calimero921/sensor_tab/src/main.h

/*
*/

#include "Arduino.h"

// See the following for generating UUIDs:
// https://www.uuidgenerator.net/
#define SERVICE_UUID "4fafc201-1fb5-459e-8fcc-c5c9c331914b"
#define LED_CHARACTERISTIC_UUID "beb5483e-36e1-4688-b7f5-ea07361b26a8"
#define RFID_CHARACTERISTIC_UUID "bb23e586-ce7c-4bc7-b3fb-b5f88a0f3277"

// configuration Adafruit_NeoPixel
#define PIXELCOUNT 9

// configuration MFRC522
#define MFRC522COUNT 9

//#define DEBUG
